FabioNMI/UltimateC64PSU/firmware/src/ac_control.h

/*
 * ac_control.h
 *
 *  Created on: Jan. 25, 2025
 *      Author: fabiop
 */

#ifndef AC_CONTROL_H_
#define AC_CONTROL_H_

#include <psu_global.h>

psu_state_t ac_control_fsm(psu_state_t new_state);

#endif /* AC_CONTROL_H_ */
