FabioNMI/UltimateC64PSU/firmware/src/logo.h

/*
 * logo.h
 *
 *  Created on: Jan. 25, 2025
 *      Author: fabiop
 */

#ifndef LOGO_H_
#define LOGO_H_

#include <hal_data.h>

#define LOGO_HEIGHT   23
#define LOGO_WIDTH    32
static const uint8_t logo[] = {
  0b00000000, 0b11111111, 0b00000000, 0b00000000,
  0b00000011, 0b11111111, 0b10000000, 0b00000000,
  0b00000111, 0b11111111, 0b10000000, 0b00000000,
  0b00001111, 0b11111111, 0b10000000, 0b00000000,
  0b00011110, 0b00000001, 0b10000000, 0b00000000,
  0b00111100, 0b00000000, 0b00000000, 0b00000000,
  0b01111000, 0b00000000, 0b00111111, 0b11110000,
  0b11110000, 0b00000000, 0b00111111, 0b11100000,
  0b11110000, 0b00000000, 0b00111111, 0b11000000,
  0b11110000, 0b00000000, 0b00111111, 0b10000000,
  0b11110000, 0b00000000, 0b00111111, 0b00000000,
  0b11110000, 0b00000000, 0b00000000, 0b00000000,
  0b11110000, 0b00000000, 0b00111111, 0b00000000,
  0b11110000, 0b00000000, 0b00111111, 0b10000000,
  0b11110000, 0b00000000, 0b00111111, 0b11000000,
  0b11110000, 0b00000000, 0b00111111, 0b11100000,
  0b01111000, 0b00000000, 0b00111111, 0b11110000,
  0b00111100, 0b00000000, 0b00000000, 0b00000000,
  0b00011111, 0b00000001, 0b10000000, 0b00000000,
  0b00001111, 0b11111111, 0b10000000, 0b00000000,
  0b00000111, 0b11111111, 0b10000000, 0b00000000,
  0b00000011, 0b11111111, 0b10000000, 0b00000000,
  0b00000000, 0b11111111, 0b00000000, 0b00000000,
};

#endif /* LOGO_H_ */
