FabioNMI/UltimateC64PSU/firmware/src/utils.h

/*
 * utils.h
 *
 *  Created on: Sep. 1, 2024
 *      Author: fabiop
 */

#ifndef UTILS_H_
#define UTILS_H_

#include "hal_data.h"

void utils_init_time(uint32_t freq);
uint32_t utils_get_time(void);

#endif /* UTILS_H_ */
